BuckBic/SeniorProject/STL_Models/Wire Tube.stl

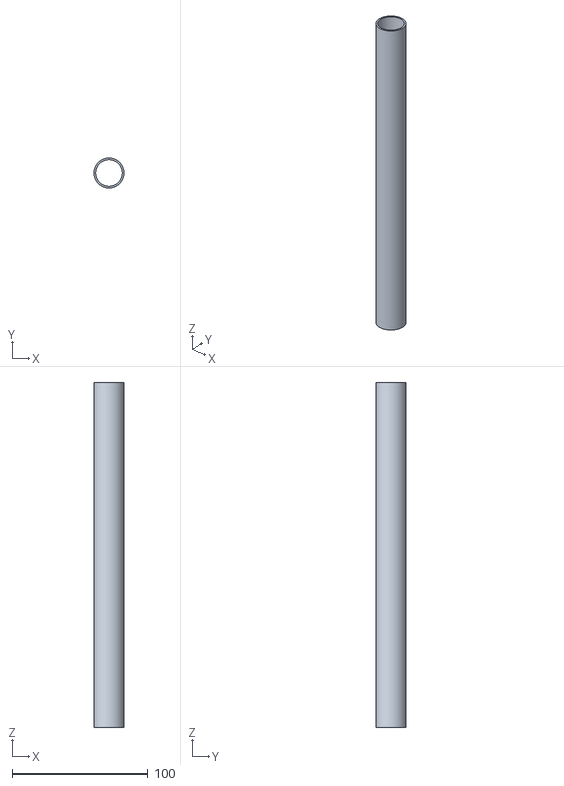
[picture p32: CAD file, 2025-05-18]
STL_Models/Wire Tube.stl
22.1 x 22.1 x 254.0
