BuckBic/SeniorProject/STL_Models/Light Sensor Mount.stl

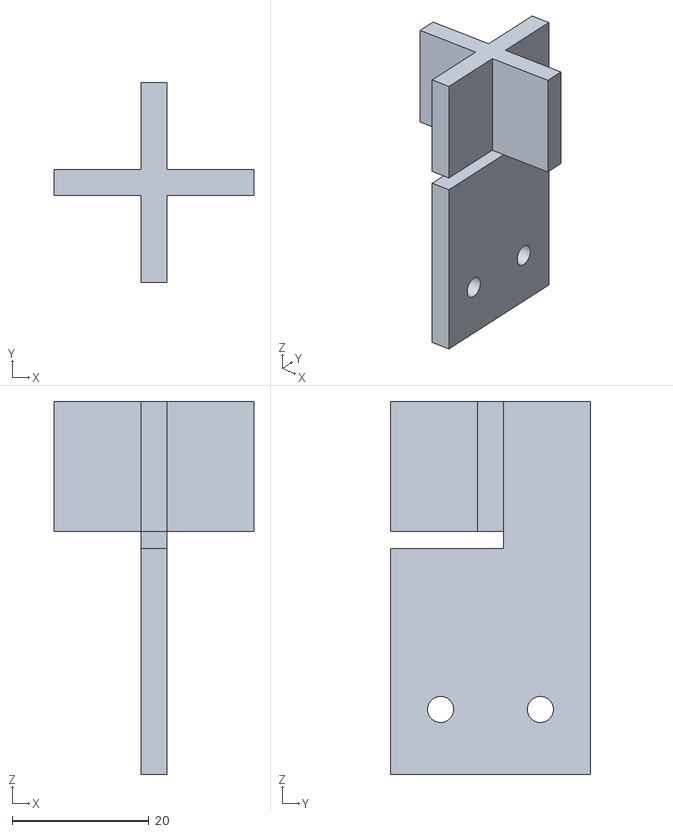
[picture p33: CAD file, 2025-05-18]
STL_Models/Light Sensor Mount.stl
29.2 x 29.2 x 54.6
