BuckBic/SeniorProject/STL_Models/Half Solar Mount No Servo.stl

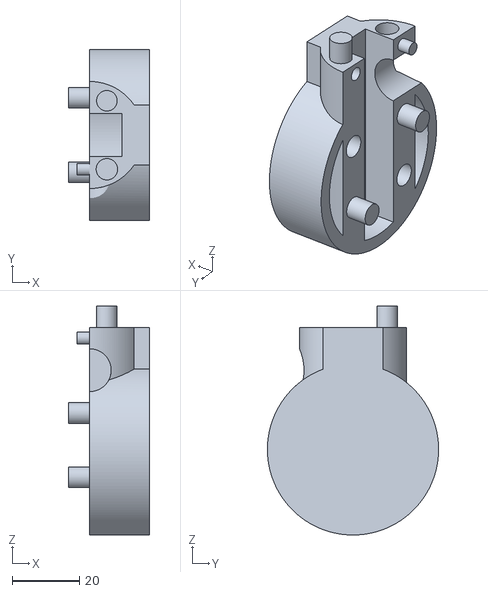
[picture p34: CAD file, 2025-05-18]
STL_Models/Half Solar Mount No Servo.stl
24.1 x 50.8 x 67.9
