BuckBic/SeniorProject/STL_Models/Feeder Load Sensor Cover.stl

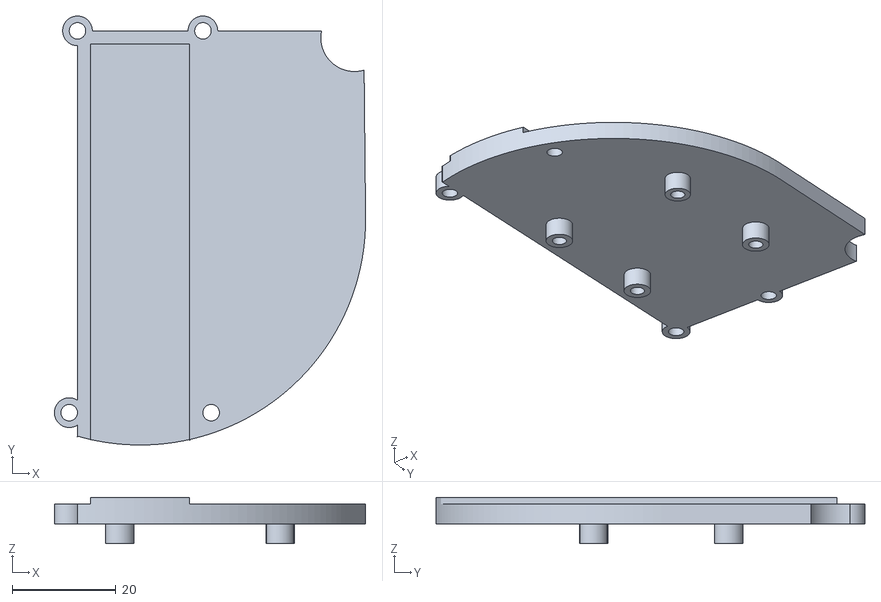
[picture p35: CAD file, 2025-05-18]
STL_Models/Feeder Load Sensor Cover.stl
59.9 x 82.5 x 8.89
