BuckBic/SeniorProject/STL_Models/Stepper plug.stl

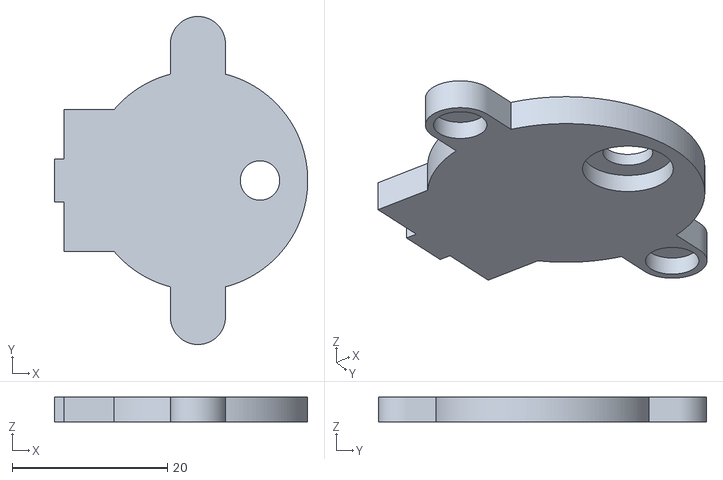
[picture p36: CAD file, 2025-05-18]
STL_Models/Stepper plug.stl
32.7 x 42.3 x 3.17
