BuckBic/SeniorProject/STL_Models/Feeder Roof Base.stl

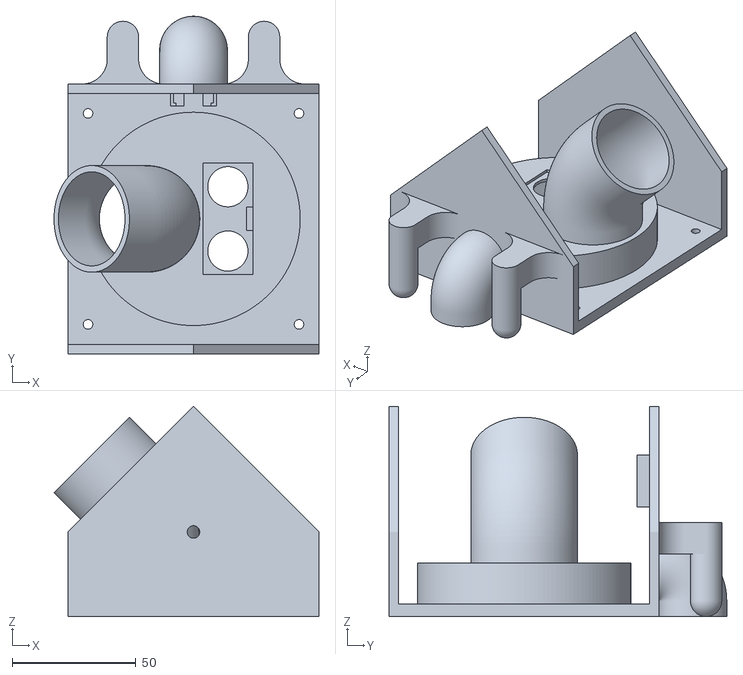
[picture p37: CAD file, 2025-05-18]
STL_Models/Feeder Roof Base.stl
107.3 x 136.7 x 85.0
