BuckBic/SeniorProject/STL_Models/Half Solar Mount With Servo.stl

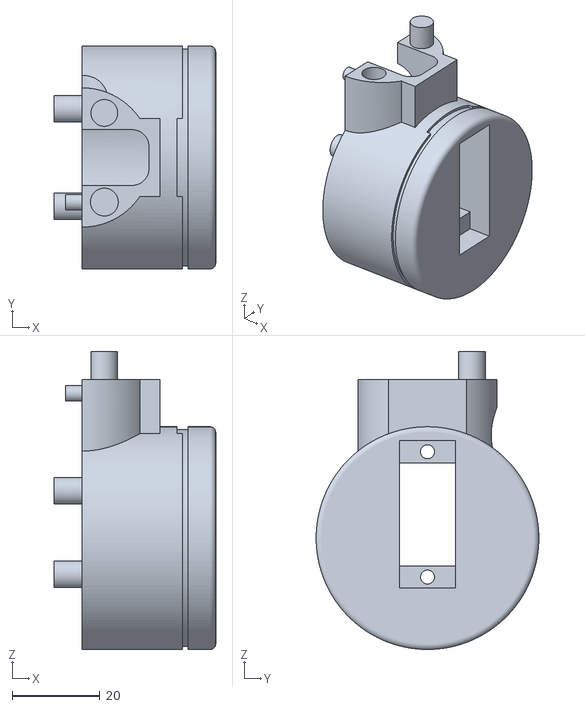
[picture p38: CAD file, 2025-05-18]
STL_Models/Half Solar Mount With Servo.stl
36.8 x 50.8 x 67.9
