BuckBic/SeniorProject/STL_Models/Wheel Spacer.stl

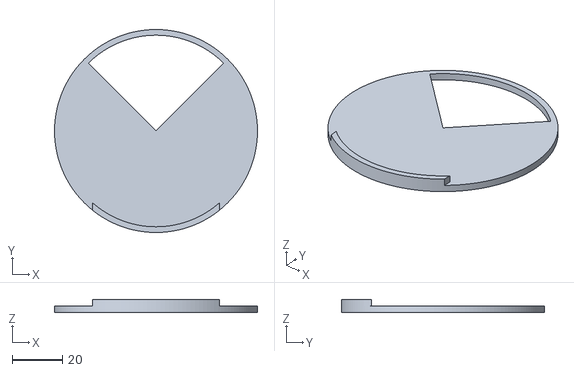
[picture p39: CAD file, 2025-05-18]
STL_Models/Wheel Spacer.stl
81.0 x 81.0 x 5.08
